linchun-yu/Timber-Living-Hinge---Design-Make-Pavilion/0.photo_source/technique1.png

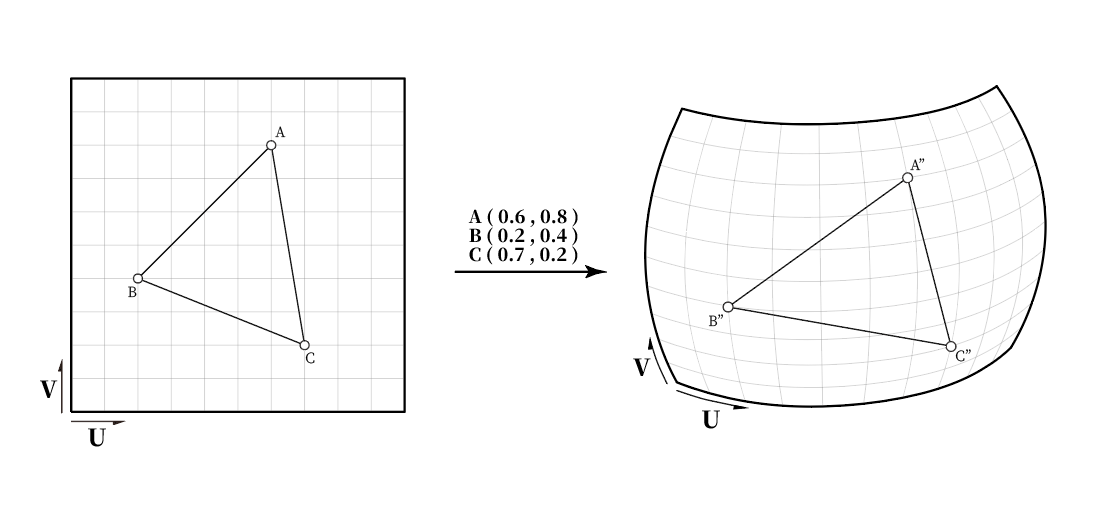
0.photo_source/technique1.png
